5hubh4m/homespan-thermostat/homespan_thermostat/identify.h

#include <HomeSpan.h>

// this class defines the identification service
class Identify: public Service::AccessoryInformation {
public:
  // constructor for the service
  Identify(
    const char* name,
    const char* manufacturer,
    const char* serialNumber,
    const char* model,
    const char* firmwareVersion
  ) {
    new Characteristic::Name(name);
    new Characteristic::Manufacturer(manufacturer);
    new Characteristic::SerialNumber(serialNumber);
    new Characteristic::Model(model);
    new Characteristic::FirmwareRevision(firmwareVersion);
    new Characteristic::Identify();
  }
};

// this class defines the protocol information
class ProtocolVersion: public Service::HAPProtocolInformation {
public:
  // constructor for the service
  ProtocolVersion(const char* version = "1.1.0") {
    new Characteristic::Version(version);
  }
};
